zeus-home/-Archived-hercules/hardware/iotssbv2_b.png

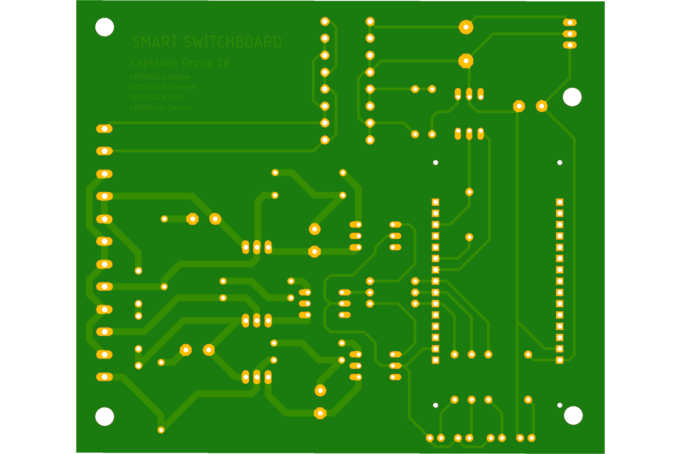
hardware/iotssbv2_b.png
