zeus-home/-Archived-hercules/hardware/PCB with captions.png

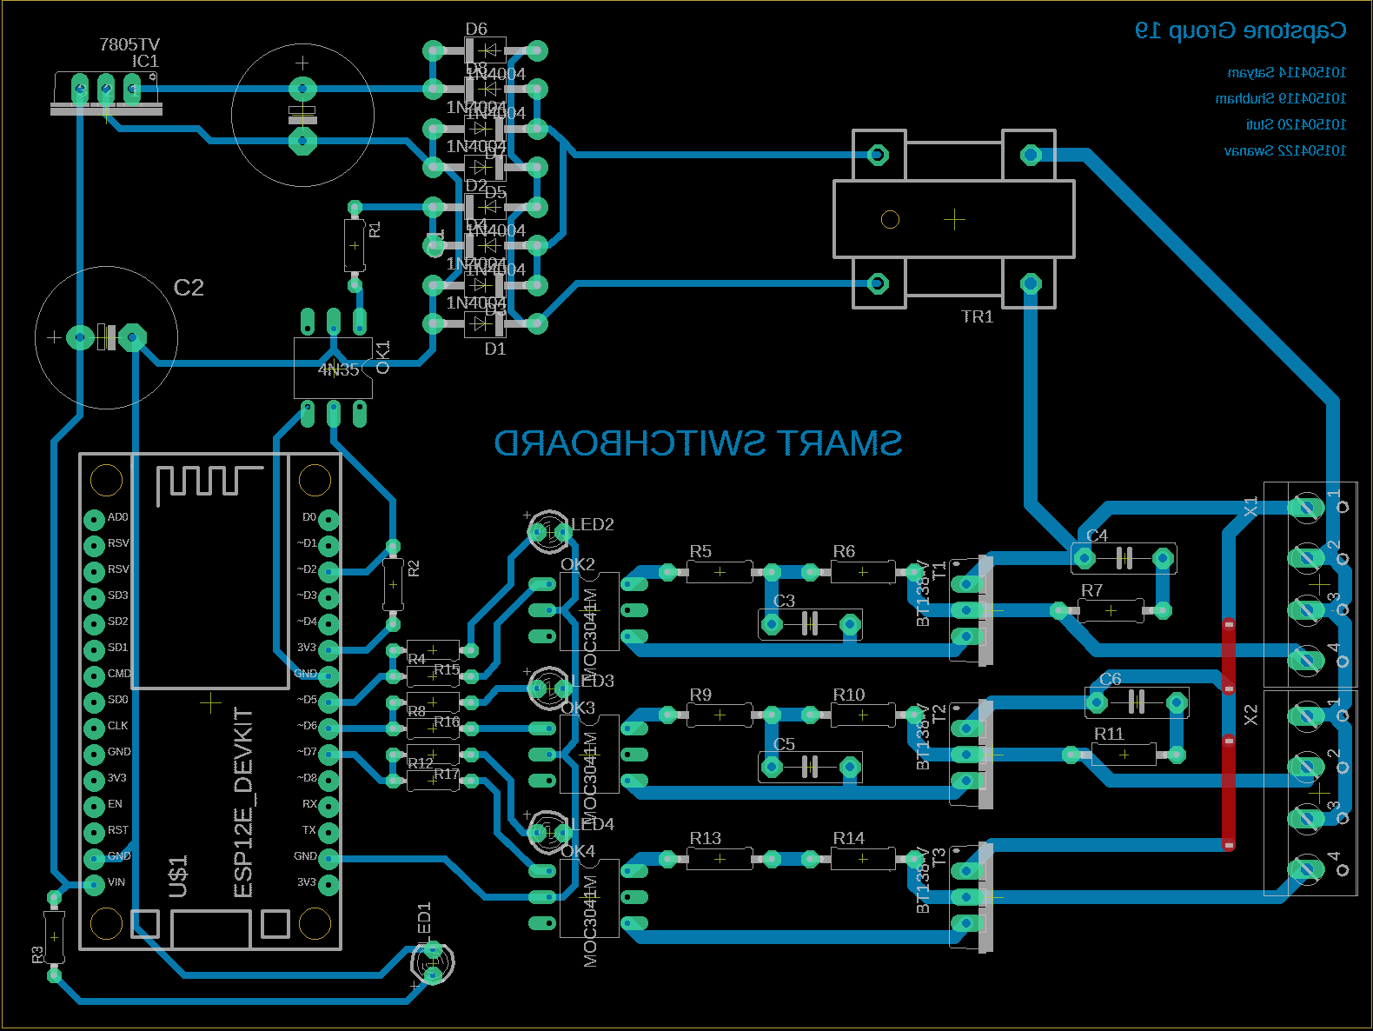
hardware/PCB with captions.png
