zeus-home/-Archived-hercules/hardware/v2_b.png

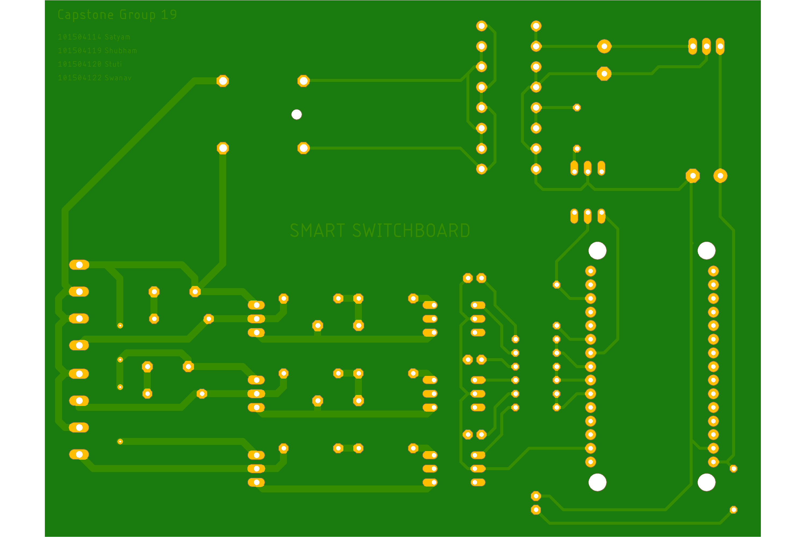
hardware/v2_b.png
